robsonsmartins/roller-transfer/img/DSC07709.JPG

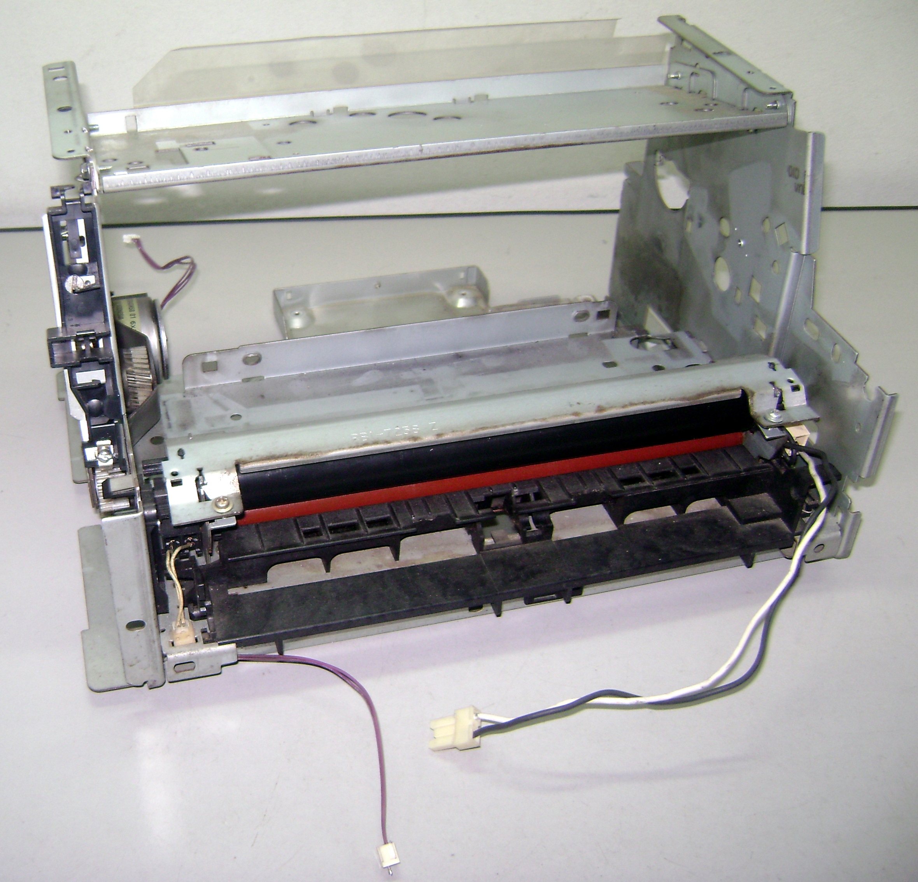
img/DSC07709.JPG
