robsonsmartins/roller-transfer/img/DSC07712.JPG

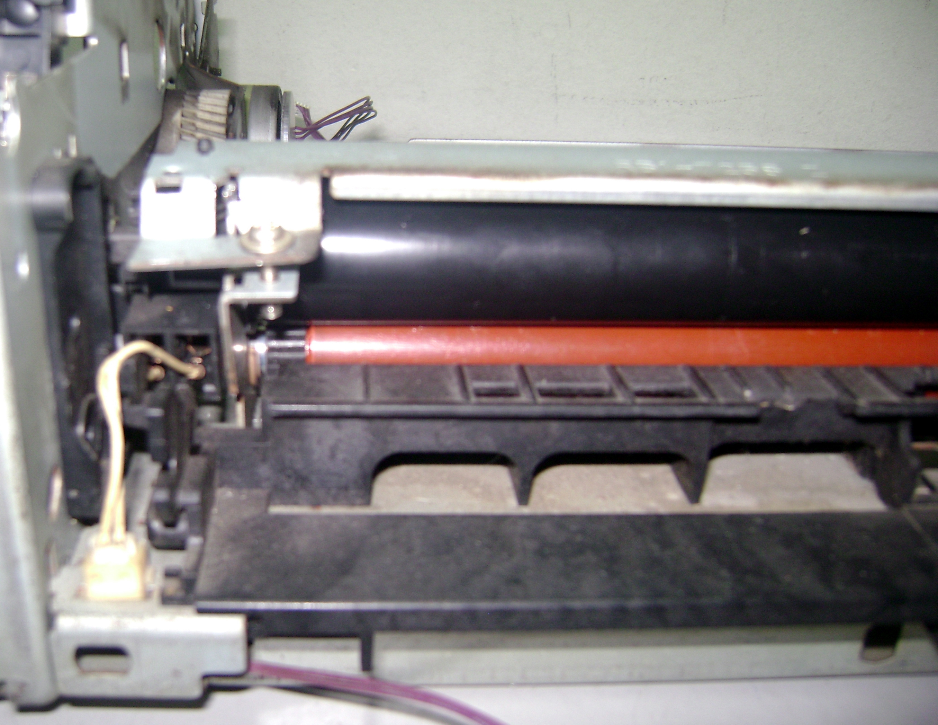
img/DSC07712.JPG
