robsonsmartins/roller-transfer/img/DSC07715.JPG

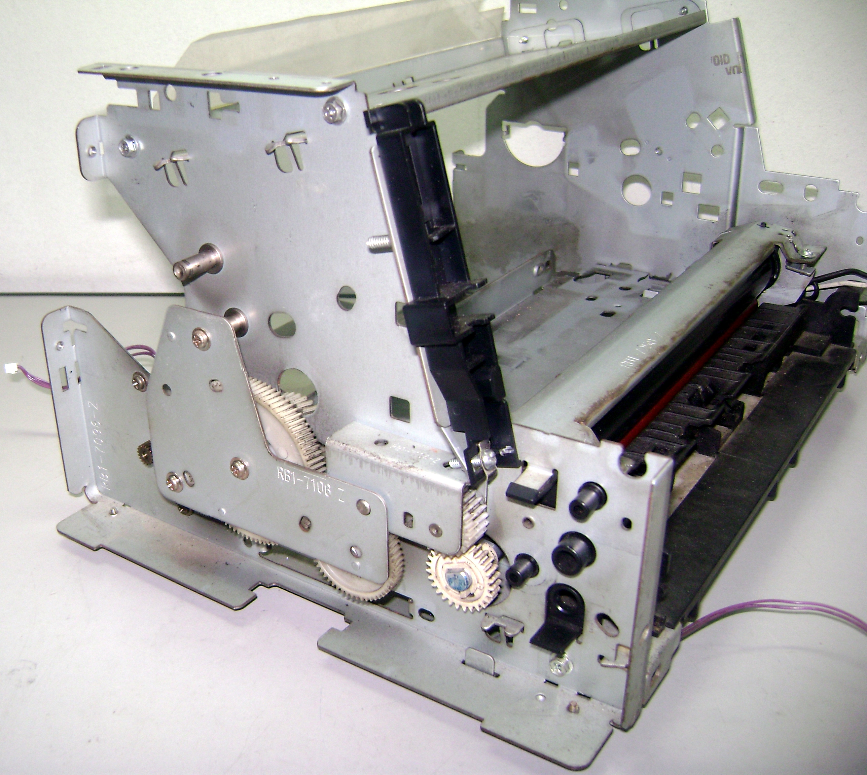
img/DSC07715.JPG
