robsonsmartins/roller-transfer/img/DSC07716.JPG

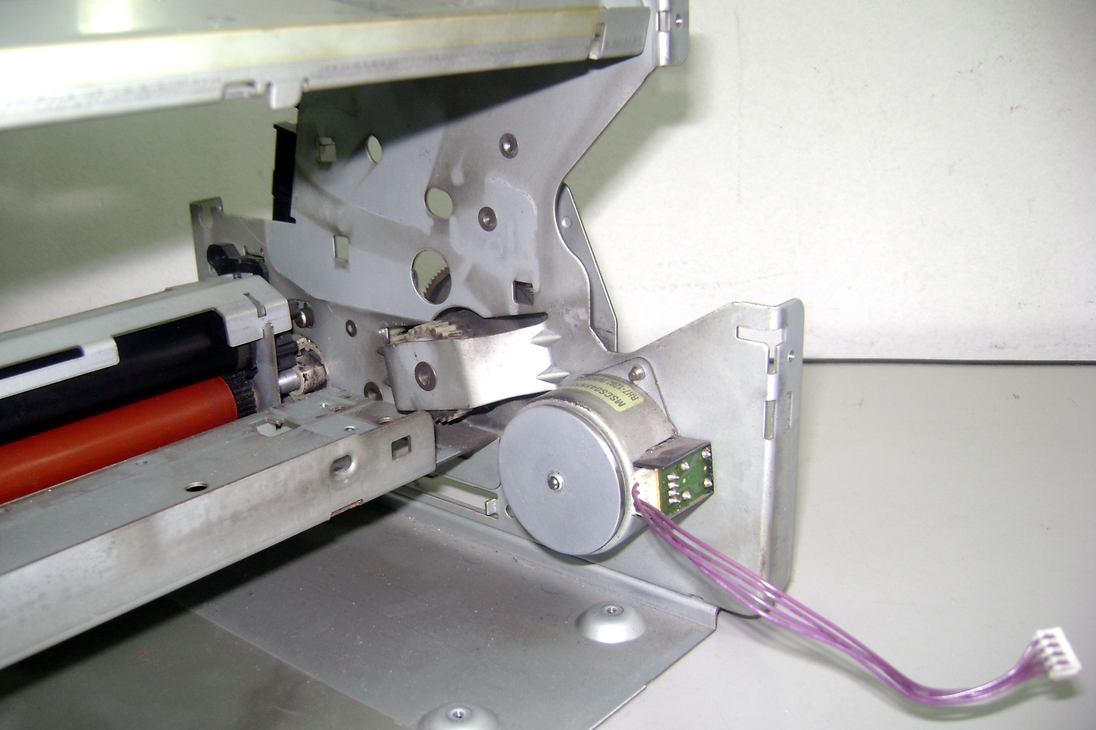
img/DSC07716.JPG
