robsonsmartins/roller-transfer/img/DSC07719.JPG

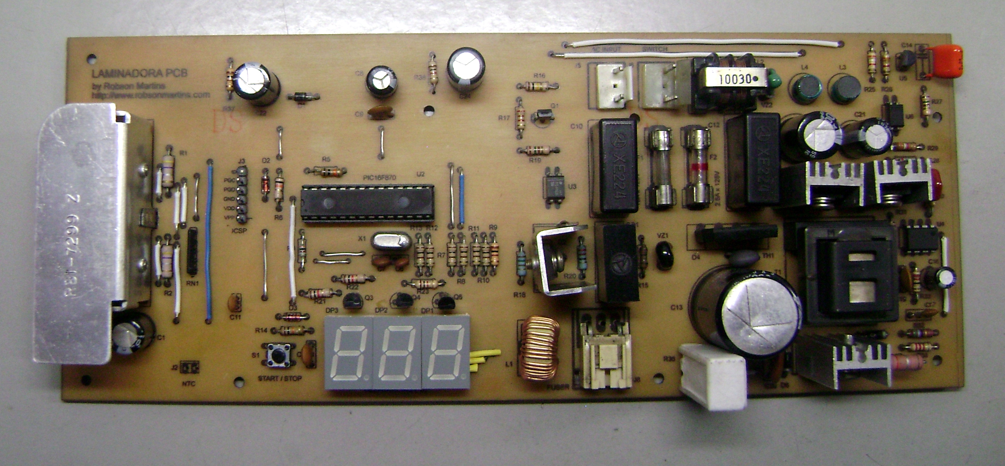
img/DSC07719.JPG
