robsonsmartins/roller-transfer/img/DSC07721.JPG

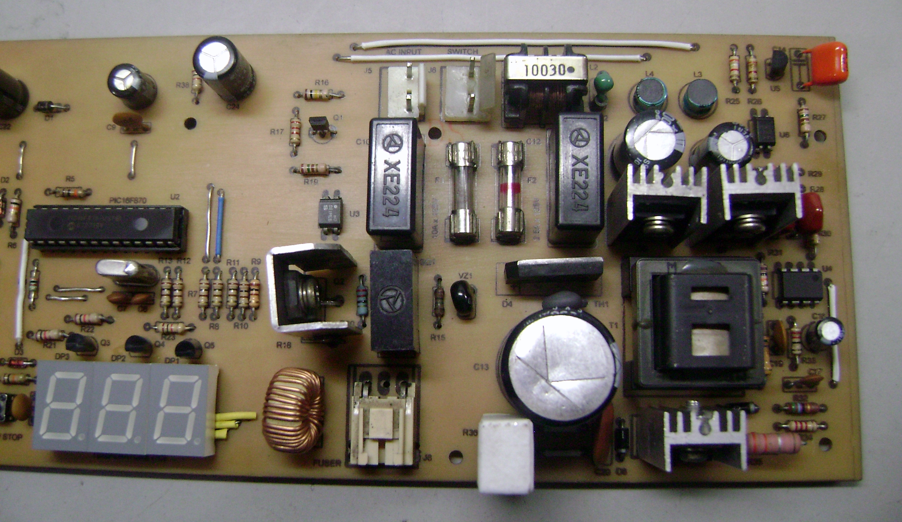
img/DSC07721.JPG
