robsonsmartins/roller-transfer/img/DSC07729.JPG

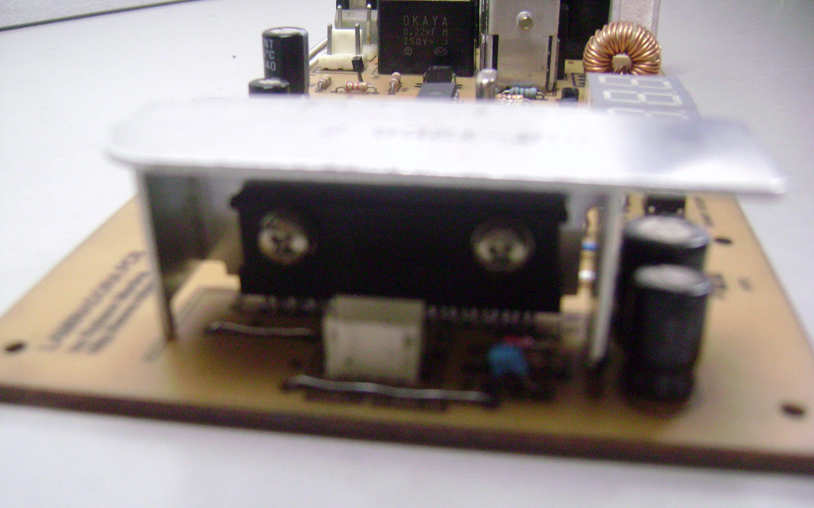
img/DSC07729.JPG
