robsonsmartins/roller-transfer/img/DSC07809.JPG

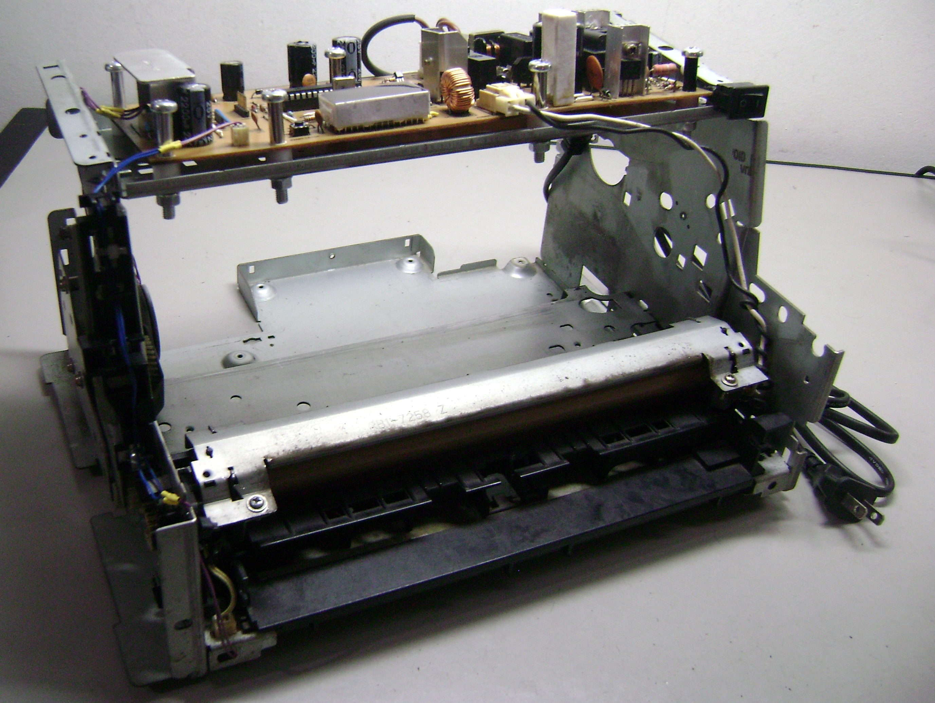
img/DSC07809.JPG
