robsonsmartins/roller-transfer/img/DSC07812.JPG

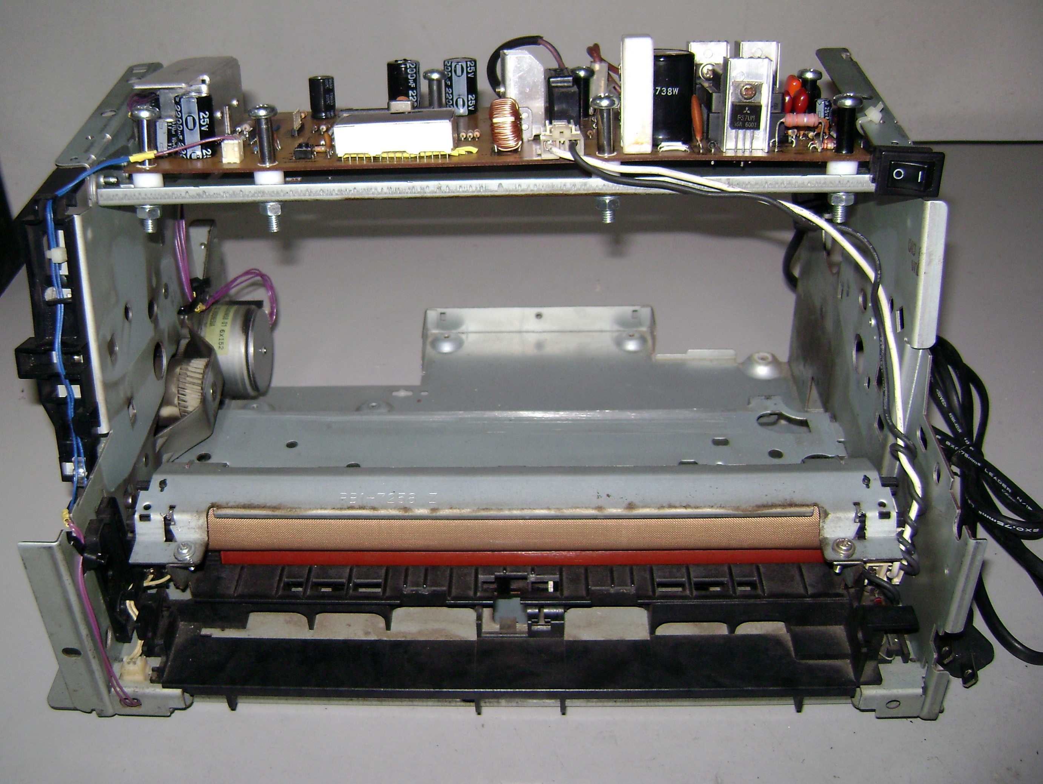
img/DSC07812.JPG
