robsonsmartins/roller-transfer/img/DSC07813.JPG

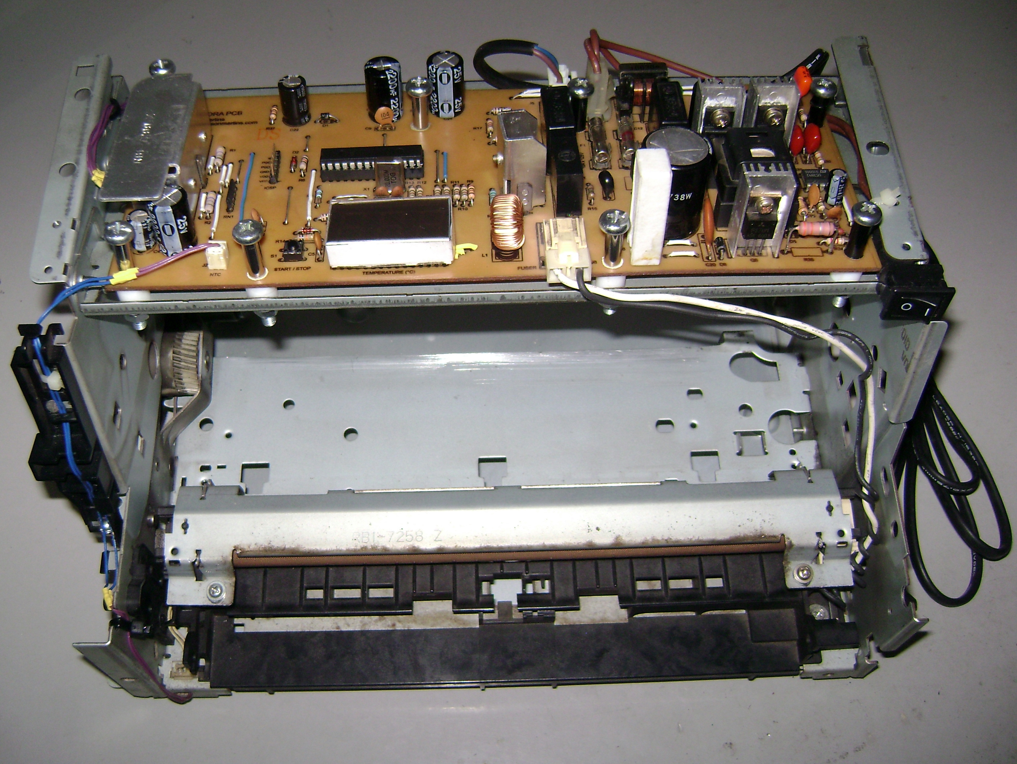
img/DSC07813.JPG
