robsonsmartins/roller-transfer/img/DSC07846.JPG

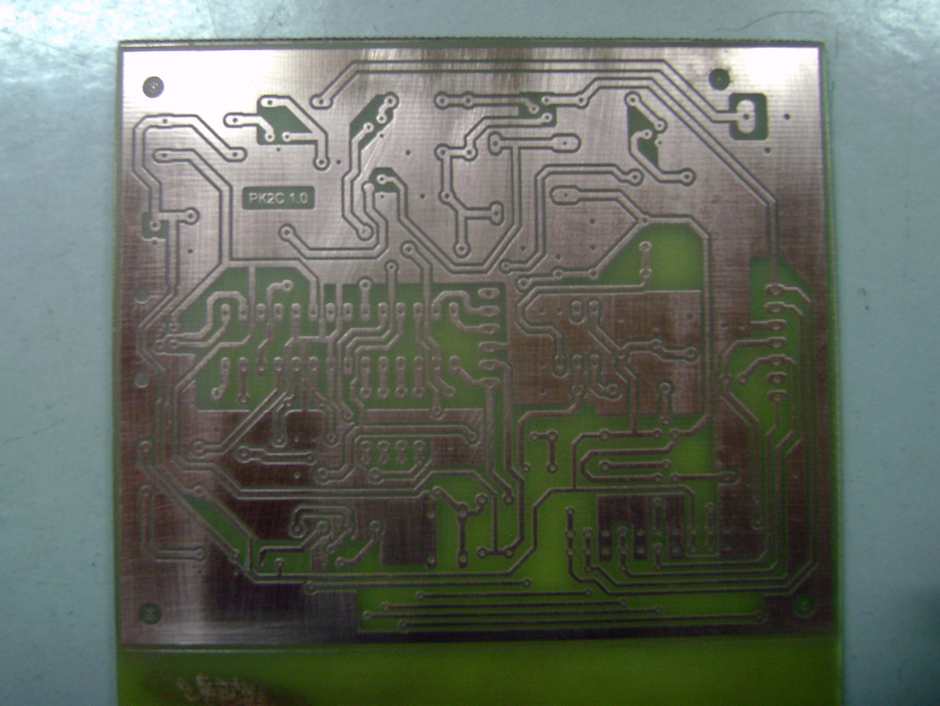
img/DSC07846.JPG
