robsonsmartins/roller-transfer/img/DSC07848.JPG

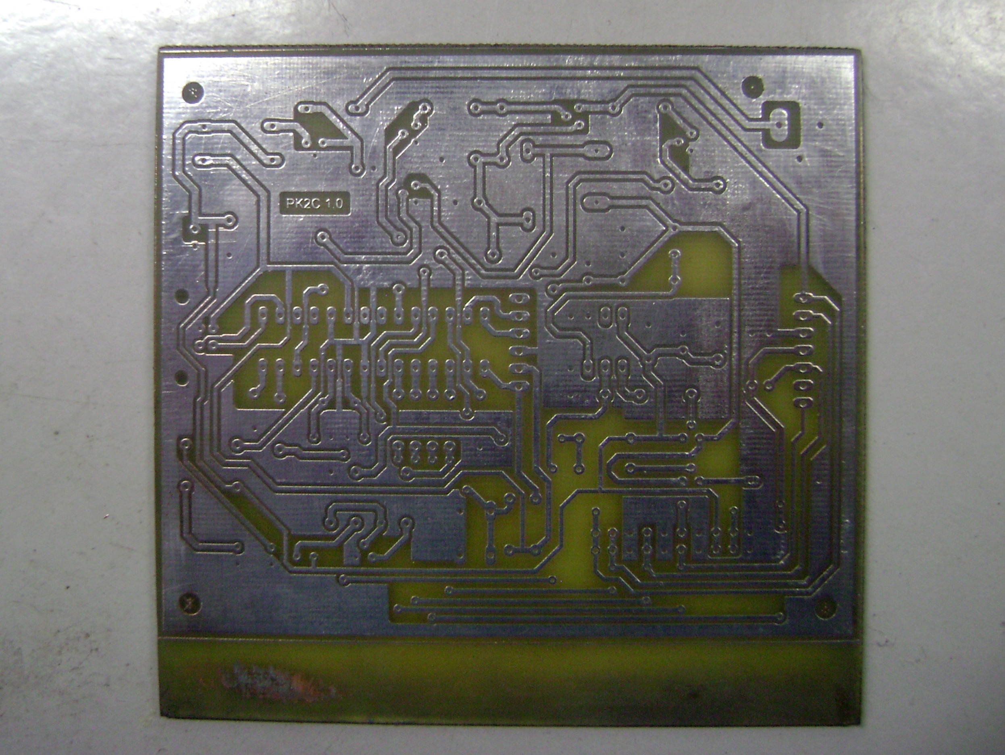
img/DSC07848.JPG
